tsmiltonAgents/pl60c-dmx-wakeup/docs/gerber_bottom_check.png

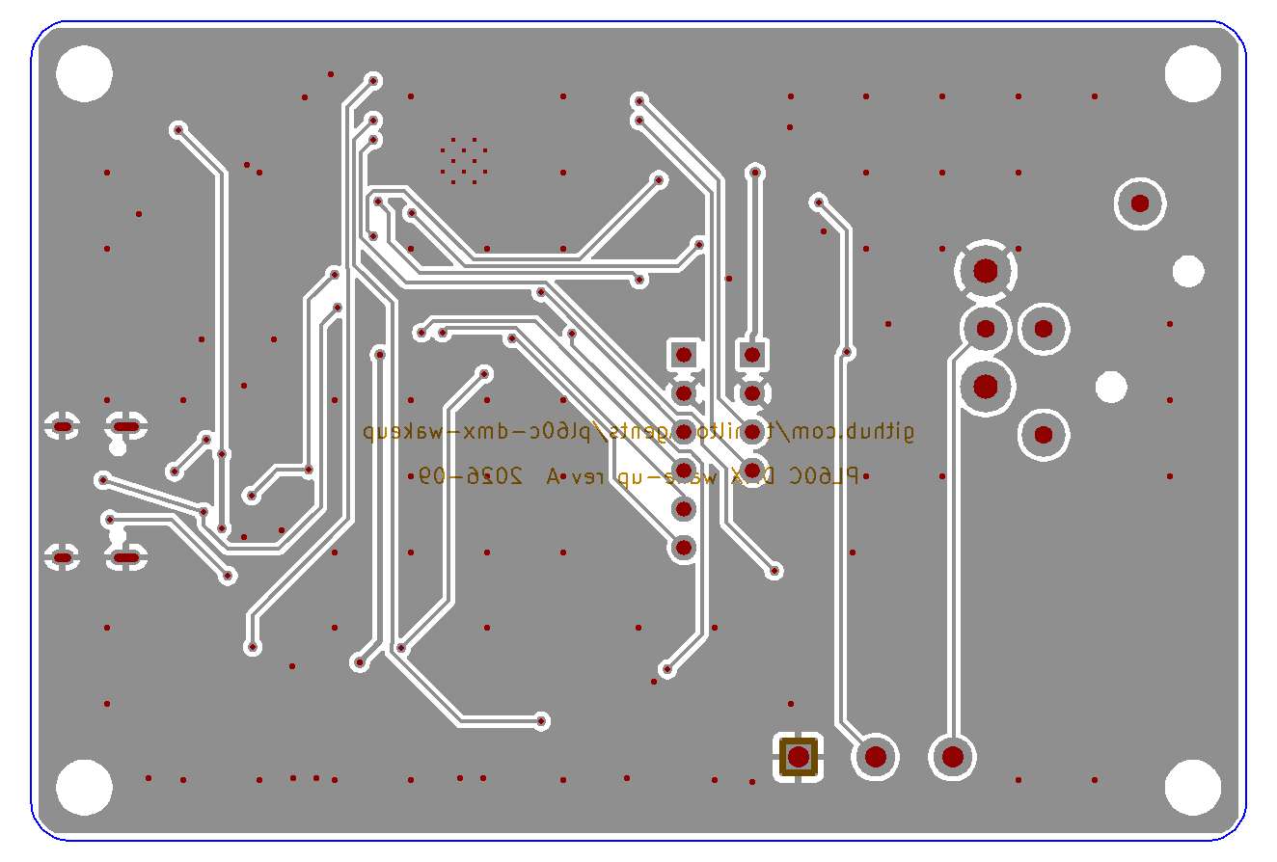
docs/gerber_bottom_check.png
