tsmiltonAgents/pl60c-dmx-wakeup/docs/mini_gerber_top_check.png

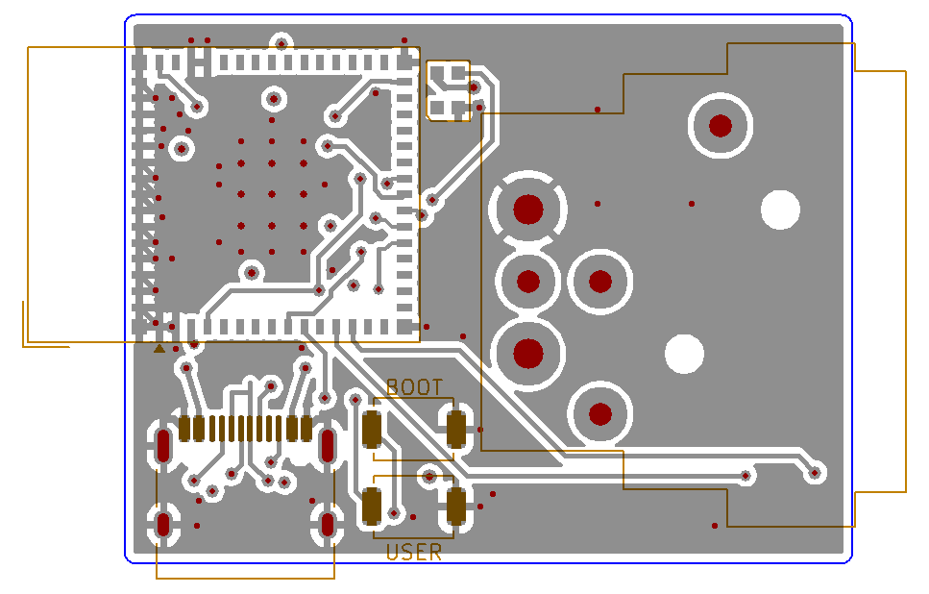
docs/mini_gerber_top_check.png
