tsmiltonAgents/pl60c-dmx-wakeup/production/render_bottom.png

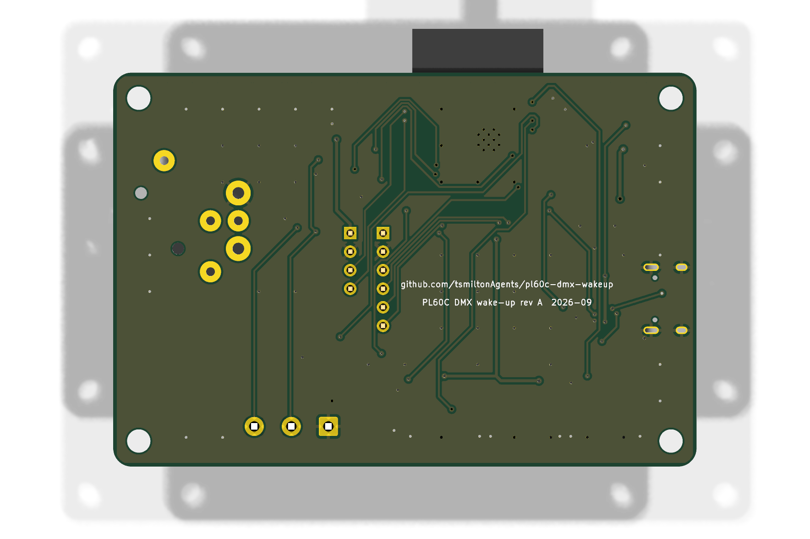
production/render_bottom.png
