tsmiltonAgents/pl60c-dmx-wakeup/build/render_top.png

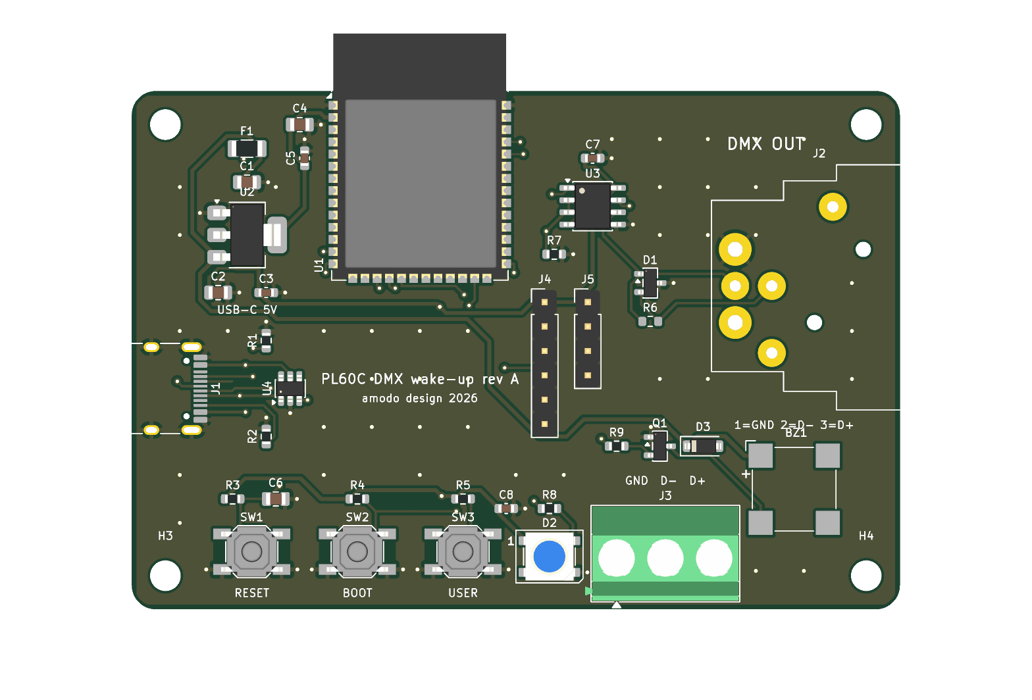
build/render_top.png
